joshajohnson/Hub16/Documents/imgs/header-img.JPG

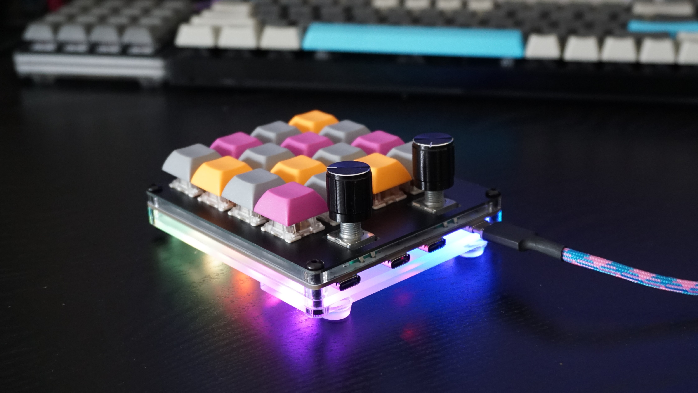
Documents/imgs/header-img.JPG
