joshajohnson/Hub16/Production/1.0-hs/photo-close.JPG

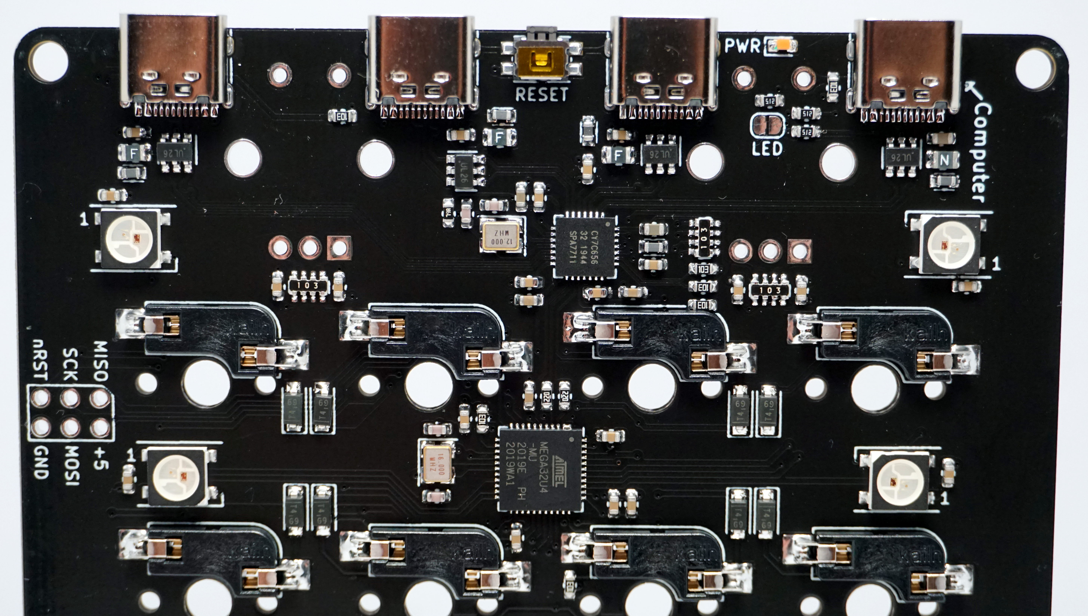
Production/1.0-hs/photo-close.JPG
