joshajohnson/Hub16/Production/1.0-hs/photo.JPG

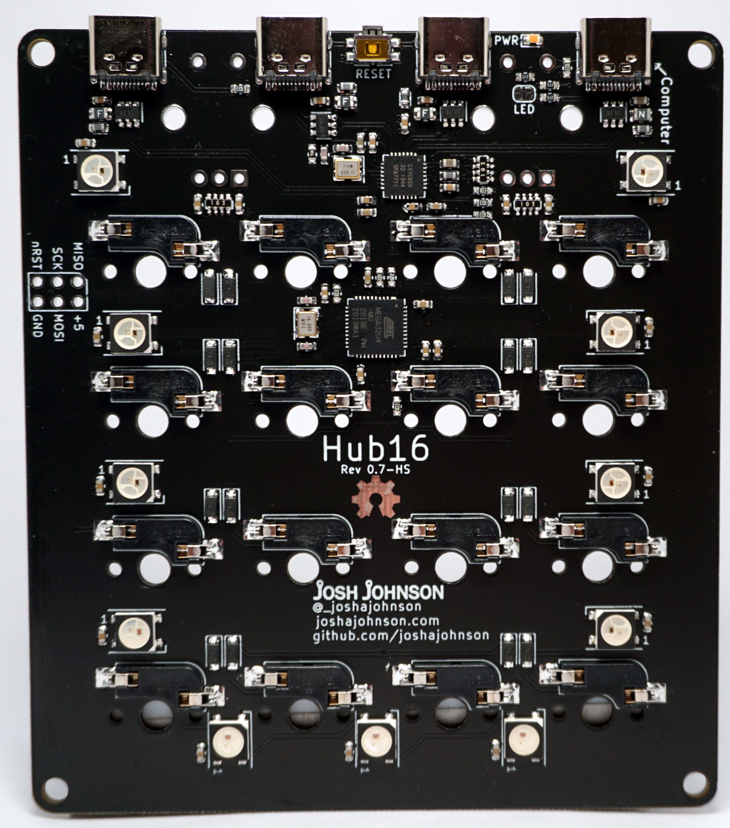
Production/1.0-hs/photo.JPG
