joshajohnson/Hub16/Production/1.0-hs/render.png

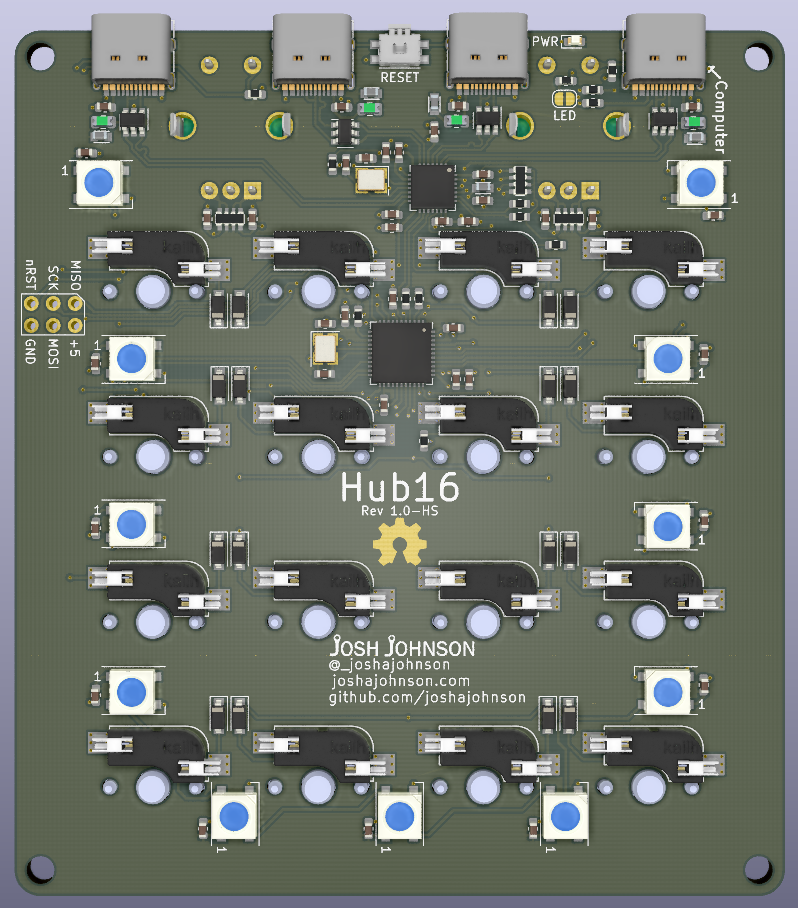
Production/1.0-hs/render.png
